LukeMet/MINIONS/Photos/Deployment/Deploy1.JPG

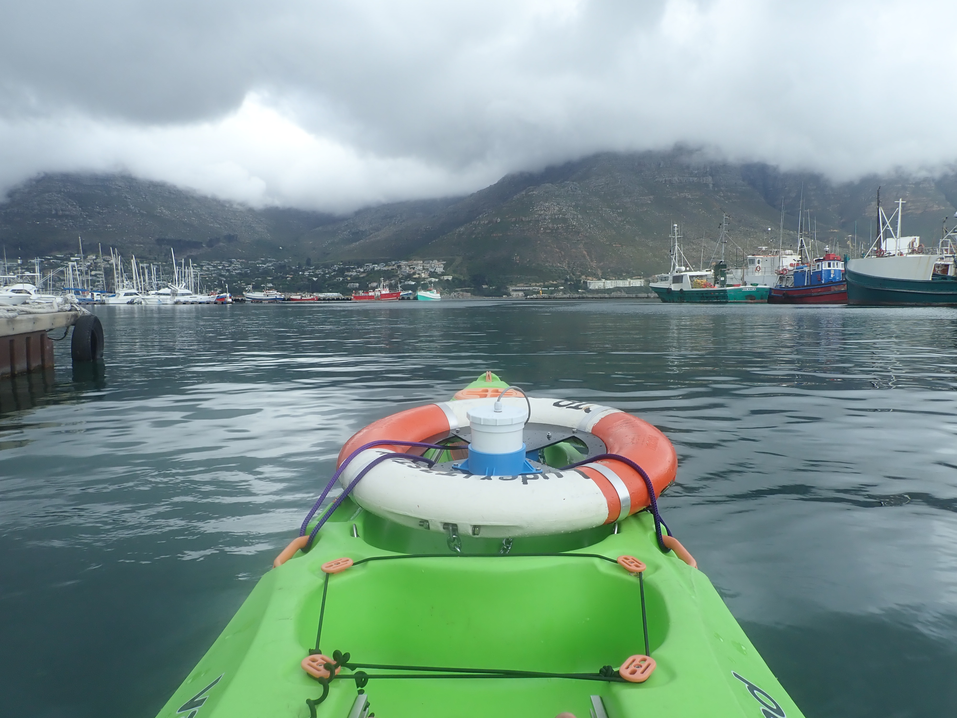
Photos/Deployment/Deploy1.JPG
