LukeMet/MINIONS/Photos/Deployment/Deploy2.JPG

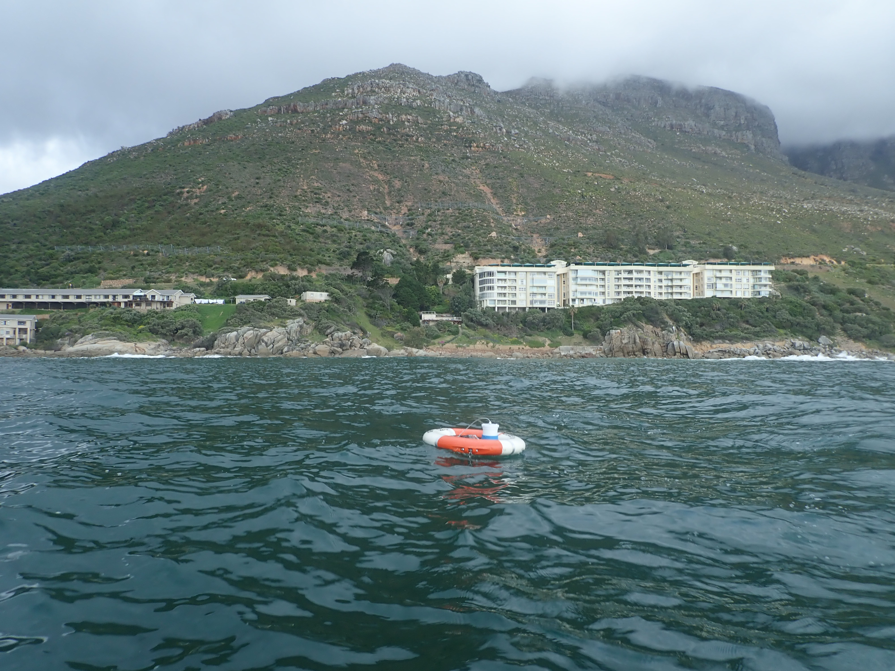
Photos/Deployment/Deploy2.JPG
