LukeMet/MINIONS/Photos/Deployment/Retreive2.JPG

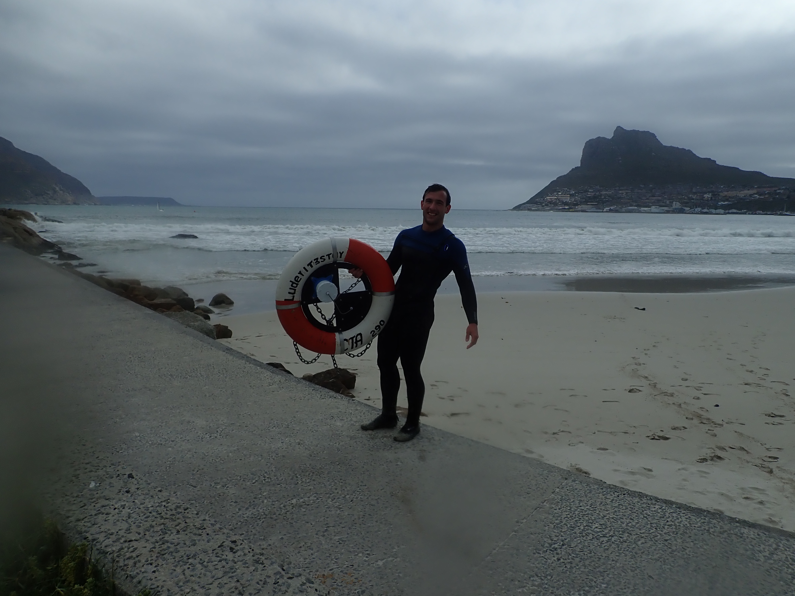
Photos/Deployment/Retreive2.JPG
