LukeMet/MINIONS/Photos/Deployment/UserInterface.jpg

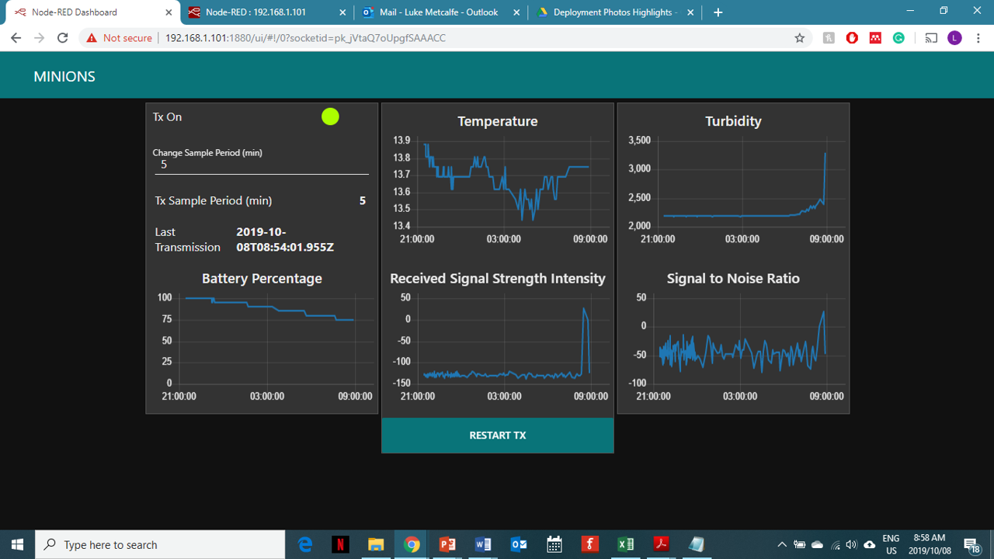
Photos/Deployment/UserInterface.jpg
