LukeMet/MINIONS/Photos/Construction/1_Upper_Microcontroller.jpg

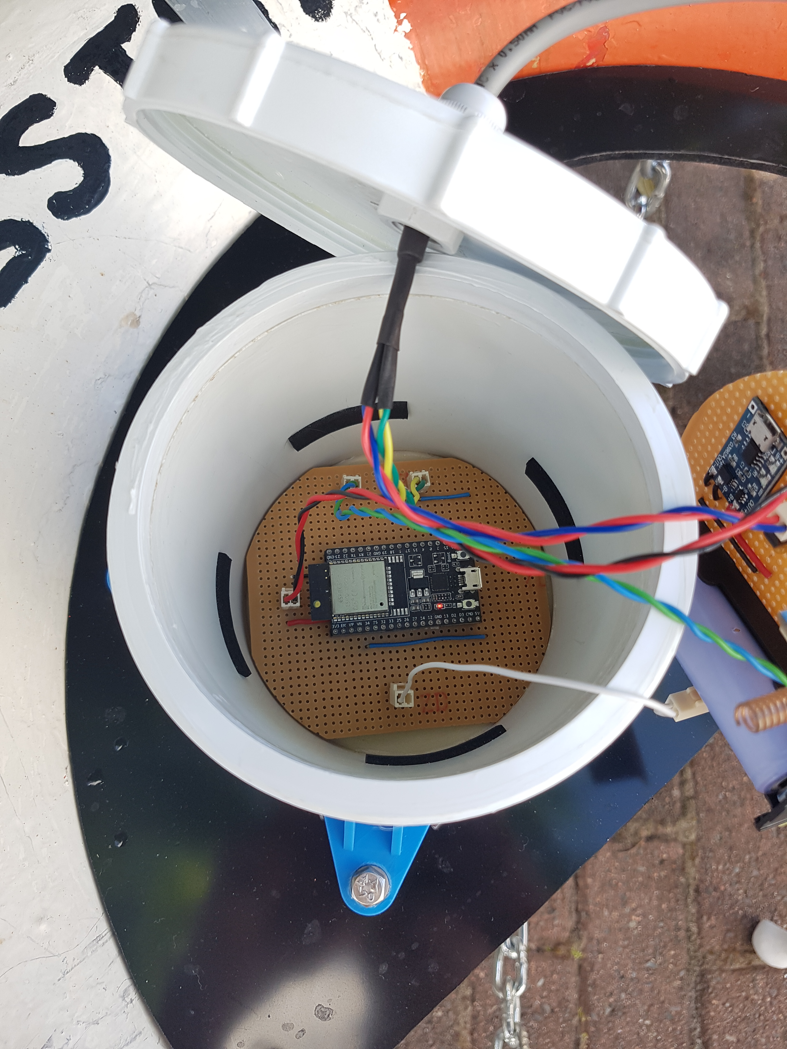
Photos/Construction/1_Upper_Microcontroller.jpg
