LukeMet/MINIONS/Photos/Construction/1_Upper_PowerModule.jpg

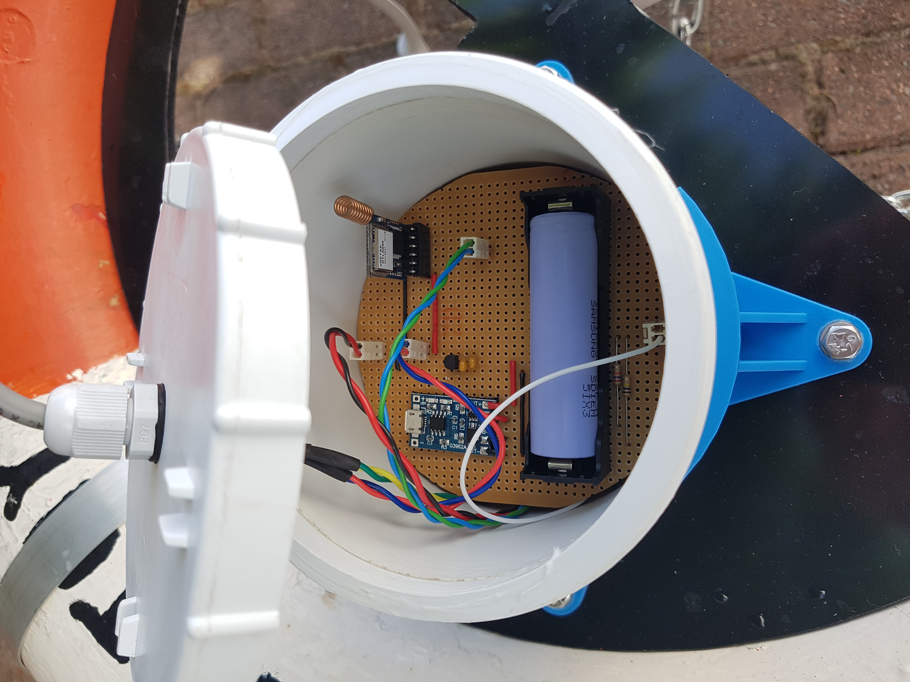
Photos/Construction/1_Upper_PowerModule.jpg
