LukeMet/MINIONS/Photos/Construction/3_Receiver(i).jpg

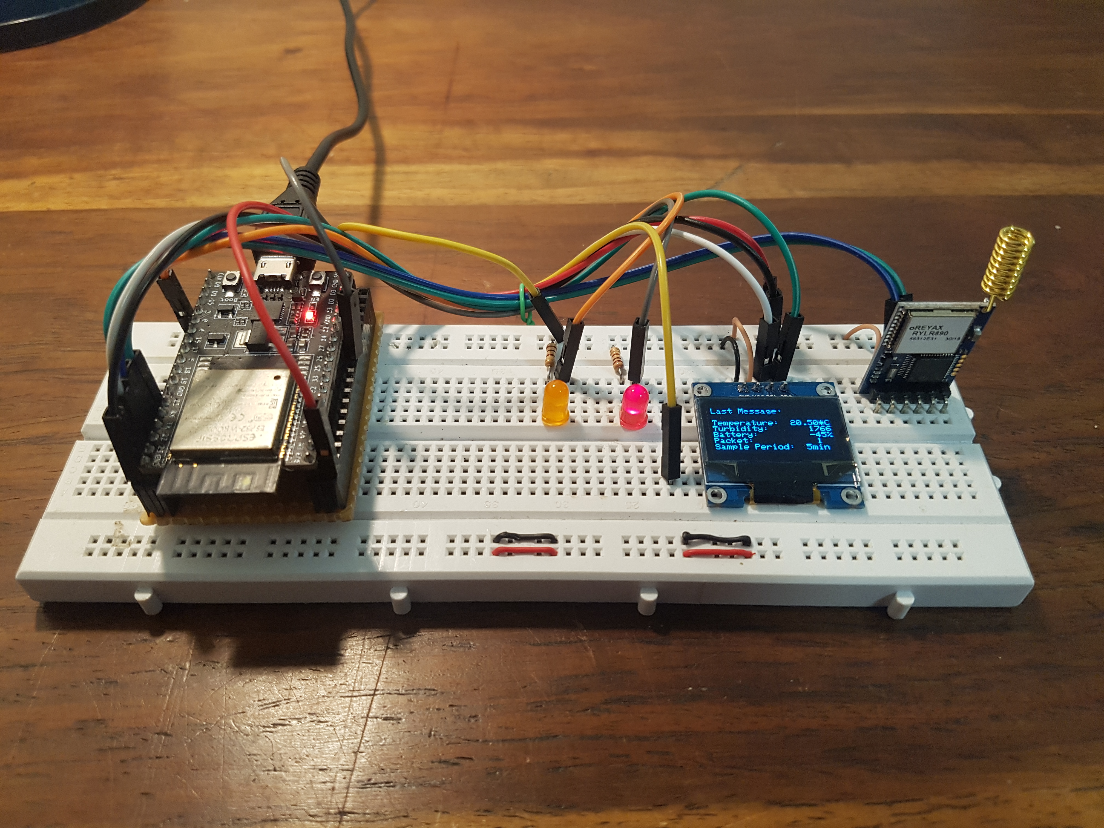
Photos/Construction/3_Receiver(i).jpg
