LukeMet/MINIONS/Photos/Construction/3_Receiver(ii).jpg

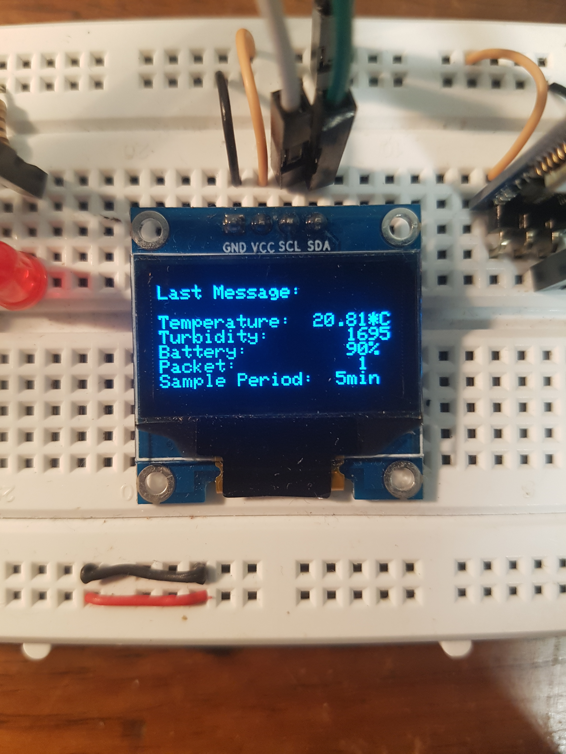
Photos/Construction/3_Receiver(ii).jpg
