LukeMet/MINIONS/Photos/Construction/2_Lower_SensorModule(ii).jpg

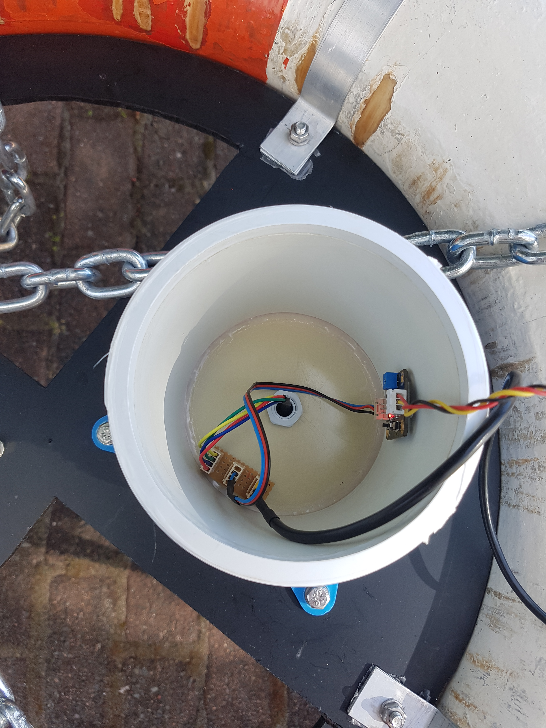
Photos/Construction/2_Lower_SensorModule(ii).jpg
